onlydcx/RCJ2023-Japan/SoftWare/OpenMV.py

import sensor, time, image, pyb, ulab
from ulab import numpy as np

sensor.reset()
sensor.set_pixformat(sensor.RGB565)
sensor.set_framesize(sensor.QVGA)
sensor.set_contrast(100)
sensor.set_brightness(1)
sensor.skip_frames(30)
sensor.set_auto_gain(False)
sensor.set_auto_whitebal(False)
sensor.set_vflip(False)
sensor.set_hmirror(True)

uart = pyb.UART(3, 19200)
usb = pyb.USB_VCP()
clock = time.clock()

distance = 0
angle = 0

def getCam(threshold):
    pixels = [0]
    rectSpace = [0]
    cnt = 0
    dx = dy = a = angle = cnt = dictance = 0

    for blob in img.find_blobs(threshold, pixels_threshold = 100, area_threshold = 100, merge = True, margin = 10):
        pixels.append(blob.pixels())
        rectSpace.append(blob.rect())
        cnt += 1

    maxVal = max(pixels)
    num = pixels.index(maxVal)

    if cnt > 0:
        dx = rectSpace[num][0] + int(rectSpace[num][2] / 2)
        dy = rectSpace[num][1] + int(rectSpace[num][3] / 2)
        distance = int(np.sqrt(pow(160 - dx,2) + pow(120 - dy,2)))
        angle = 90 - int(np.degrees(np.arctan2(120 - dy,dx - 160)))
        a = (120 - dy) / (dx - 160)
        if angle < 0:
            angle += 360

    return angle, dx, dy, a, cnt, distance

while True:
    try:
        clock.tick()
        img = sensor.snapshot()
        #data = getCam([(0, 100, -3, 15, -35, -13)])
        data = getCam([(0, 100, -128, 127, 17, 127)])
        dis = data[5]

        goal = -1

        if data[4] >= 0:
            goal = data[0]

        #print(goal,dis)

        if usb.isconnected():
            img.draw_cross(160,120,(0,0,0))
            img.draw_circle(160,120,120,(255,255,255))
            img.draw_line(160,120,blue[1],blue[2],(0,0,0))

        uart.write(str(goal)+' '+str(dis)+'\0')

    except (ZeroDivisionError, RuntimeError, OSError, NameError) as err:
        if usb.isconnected():
            print(err)
        pass
